nominetresearch/pips/hardware/casing/rendered/pip_box_assembly.png

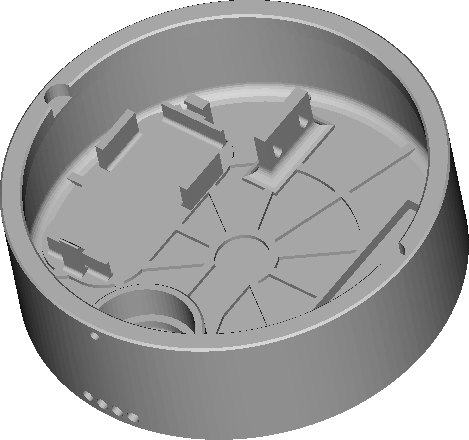
hardware/casing/rendered/pip_box_assembly.png
